cristianchelu/esphome-litterbox-monitor/tools/cad/foot.FCStd

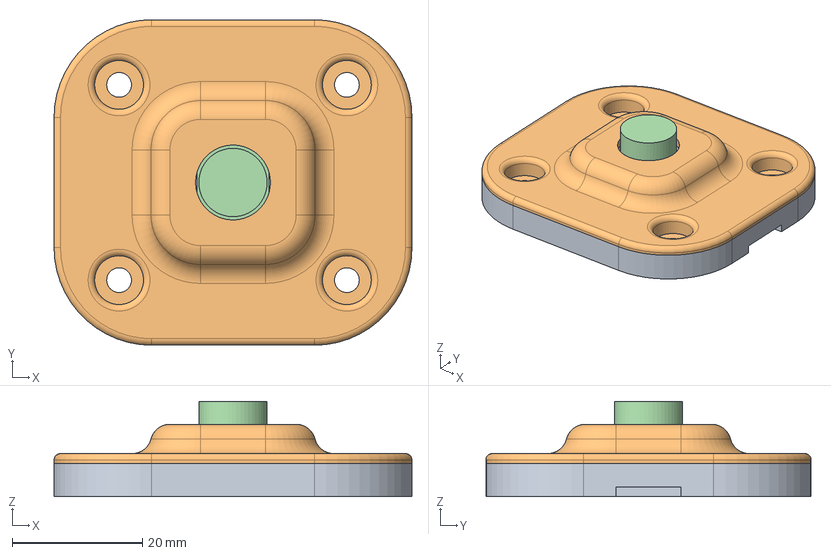
[picture p19: CAD file, 2026-09-12]
tools/cad/foot.FCStd
55.0 x 50.0 x 14.6 mm
Base
Cap
CellMetal_ref
CellFoot_ref
