cristianchelu/esphome-litterbox-monitor/tools/cad/channel_foot_2of2_162mm.stl

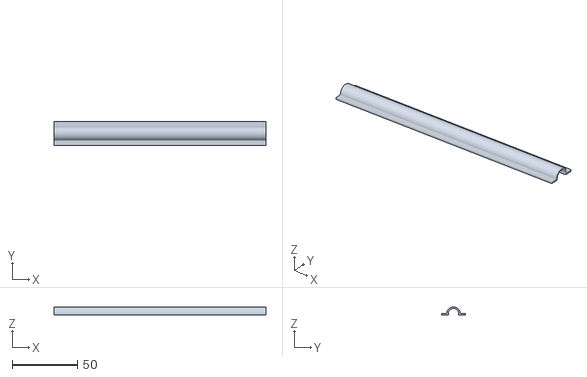
[picture p20: CAD file, 2026-09-12]
tools/cad/channel_foot_2of2_162mm.stl
161.9 x 18.4 x 6.20
