cristianchelu/esphome-litterbox-monitor/tools/cad/brain_shell_top.step

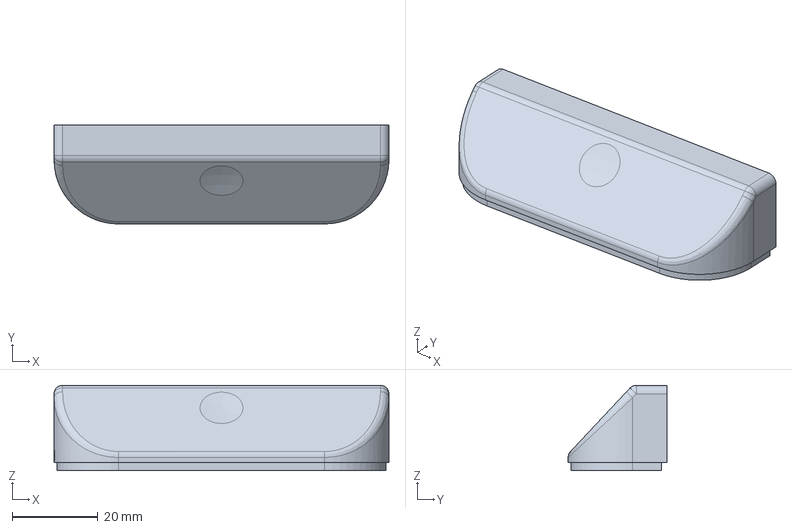
[picture p21: CAD file, 2026-09-12]
tools/cad/brain_shell_top.step
78.0 x 23.0 x 19.9 mm
