cristianchelu/esphome-litterbox-monitor/tools/cad/hx711_tray.step

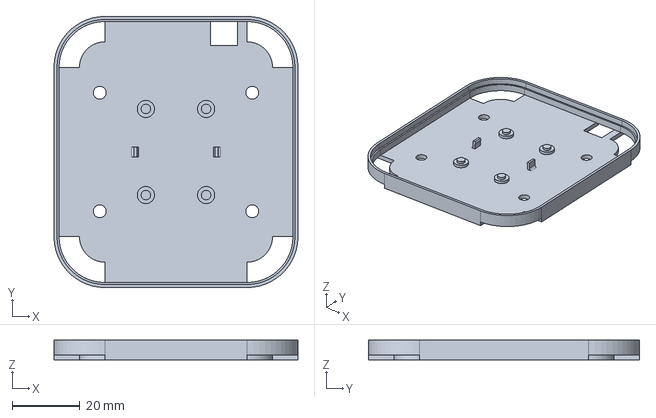
[picture p22: CAD file, 2026-09-12]
tools/cad/hx711_tray.step
72.0 x 80.0 x 5.90 mm
