cristianchelu/esphome-litterbox-monitor/tools/cad/hx711_cap.step

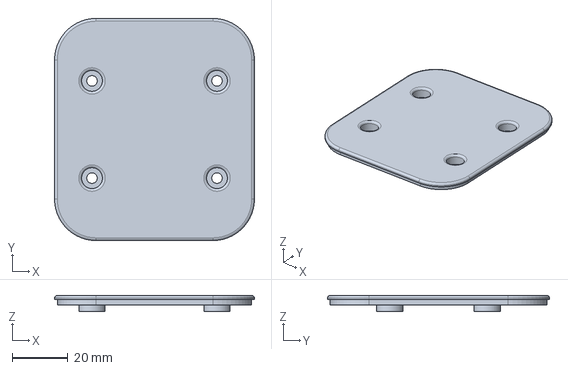
[picture p23: CAD file, 2026-09-12]
tools/cad/hx711_cap.step
72.0 x 80.0 x 5.80 mm
